wlyoung/Shelter20/Shelter20_files/DXF_Files/endwall (optional)/threequarter/door and trim A_cut2.dxf

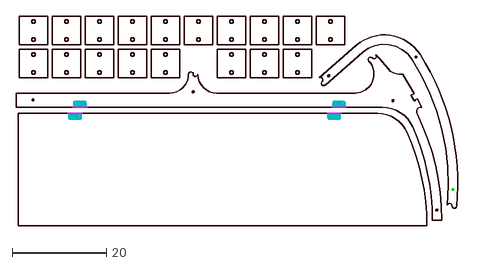
[picture p15: CAD file, 2013-10-11]
Shelter20_files/DXF_Files/endwall (optional)/threequarter/door and trim A_cut2.dxf
94.5 x 44.4
