wlyoung/Shelter20/ShippingCrate_files/DXF_Files/crate top cut 1.dxf

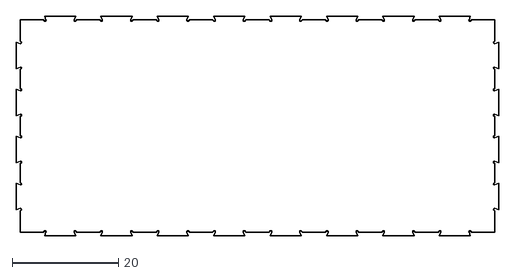
[picture p17: CAD file, 2013-10-26]
ShippingCrate_files/DXF_Files/crate top cut 1.dxf
91.0 x 41.5
