wlyoung/Shelter20/Shelter20_files/DXF_Files/threequarter inch/joists_cut2.dxf

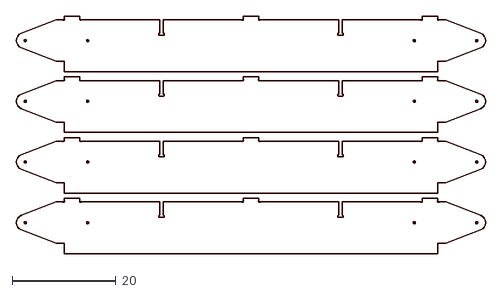
[picture p19: CAD file, 2013-10-11]
Shelter20_files/DXF_Files/threequarter inch/joists_cut2.dxf
90.4 x 45.8
