wlyoung/Shelter20/Shelter20_files/DXF_Files/threequarter inch/edge floor short A_cut1.dxf

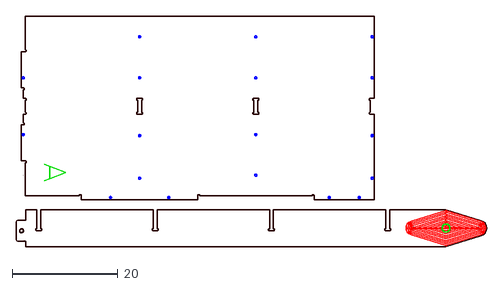
[picture p20: CAD file, 2013-10-11]
Shelter20_files/DXF_Files/threequarter inch/edge floor short A_cut1.dxf
89.0 x 43.5
