wlyoung/Shelter20/Shelter20_files/DXF_Files/threequarter inch/center floor long B_cut1.dxf

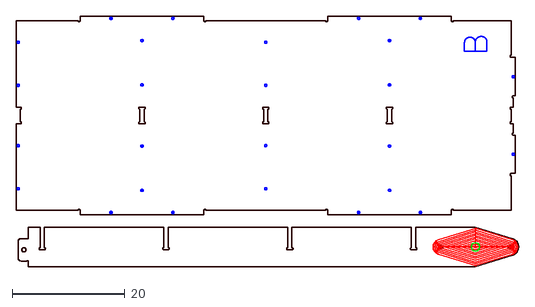
[picture p21: CAD file, 2013-10-11]
Shelter20_files/DXF_Files/threequarter inch/center floor long B_cut1.dxf
89.4 x 44.5
