wlyoung/Shelter20/Shelter20_files/DXF_Files/threequarter inch/six sleeper faces_cut1.dxf

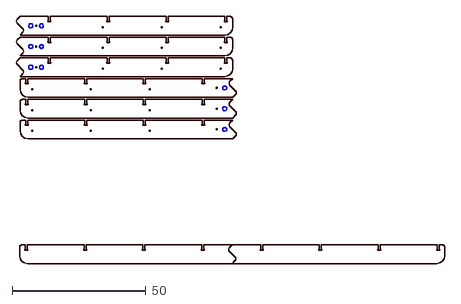
[picture p23: CAD file, 2013-10-11]
Shelter20_files/DXF_Files/threequarter inch/six sleeper faces_cut1.dxf
160.3 x 92.4
