wlyoung/Shelter20/Shelter20_files/DXF_Files/threequarter inch/four floor and two wall stringers_cut1.dxf

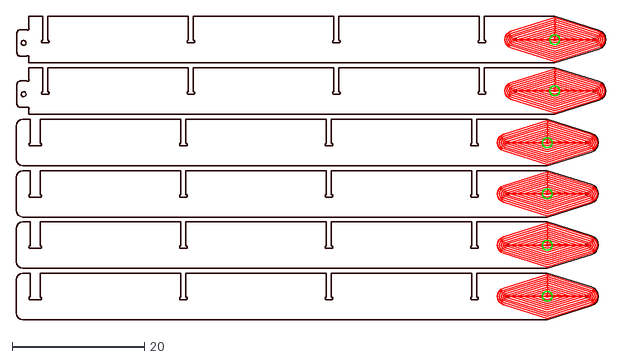
[picture p24: CAD file, 2013-10-11]
Shelter20_files/DXF_Files/threequarter inch/four floor and two wall stringers_cut1.dxf
89.1 x 45.8
