wlyoung/Shelter20/Shelter20_files/DXF_Files/threequarter inch/two sleeper face and eight short cores_cut1.dxf

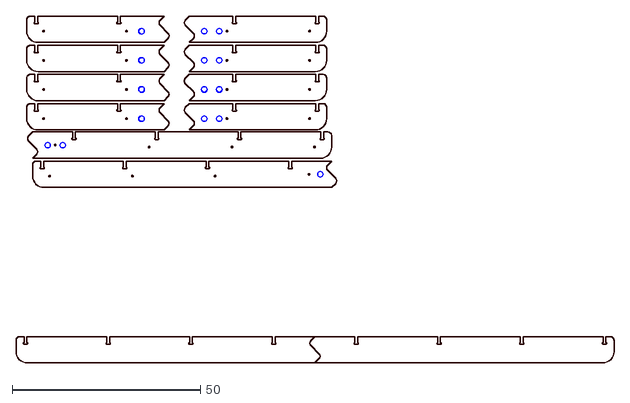
[picture p25: CAD file, 2013-10-11]
Shelter20_files/DXF_Files/threequarter inch/two sleeper face and eight short cores_cut1.dxf
159.0 x 92.2
