wlyoung/Shelter20/Shelter20_files/DXF_Files/threequarter inch/ribs_cut8.dxf

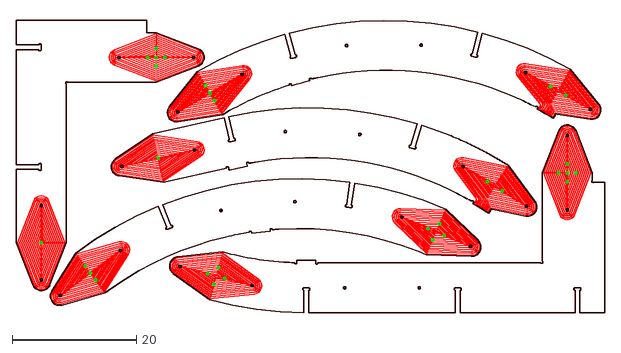
[picture p26: CAD file, 2013-10-11]
Shelter20_files/DXF_Files/threequarter inch/ribs_cut8.dxf
94.6 x 47.7
