wlyoung/Shelter20/Shelter20_files/DXF_Files/threequarter inch/six wall stringers_cut2.dxf

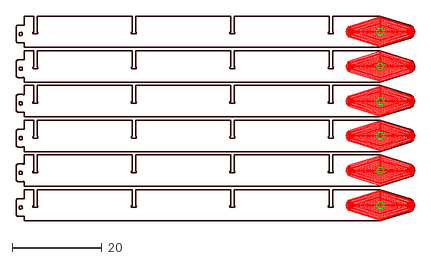
[picture p27: CAD file, 2013-10-11]
Shelter20_files/DXF_Files/threequarter inch/six wall stringers_cut2.dxf
89.0 x 45.8
