wlyoung/Shelter20/Shelter20_files/DXF_Files/threequarter inch/edge floor long C_cut1.dxf

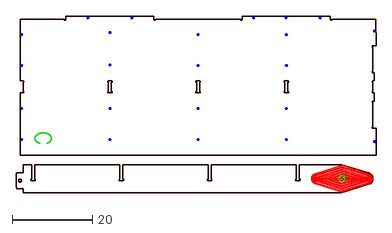
[picture p28: CAD file, 2013-10-11]
Shelter20_files/DXF_Files/threequarter inch/edge floor long C_cut1.dxf
89.8 x 44.0
