wlyoung/Shelter20/Shelter20_files/DXF_Files/threequarter inch/center floor short B_cut1.dxf

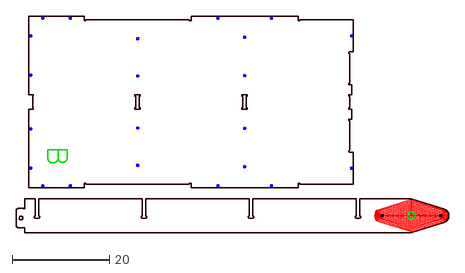
[picture p29: CAD file, 2013-10-11]
Shelter20_files/DXF_Files/threequarter inch/center floor short B_cut1.dxf
89.0 x 44.5
